sarg/keyboard/photos/IMG_20200824_121157.jpg

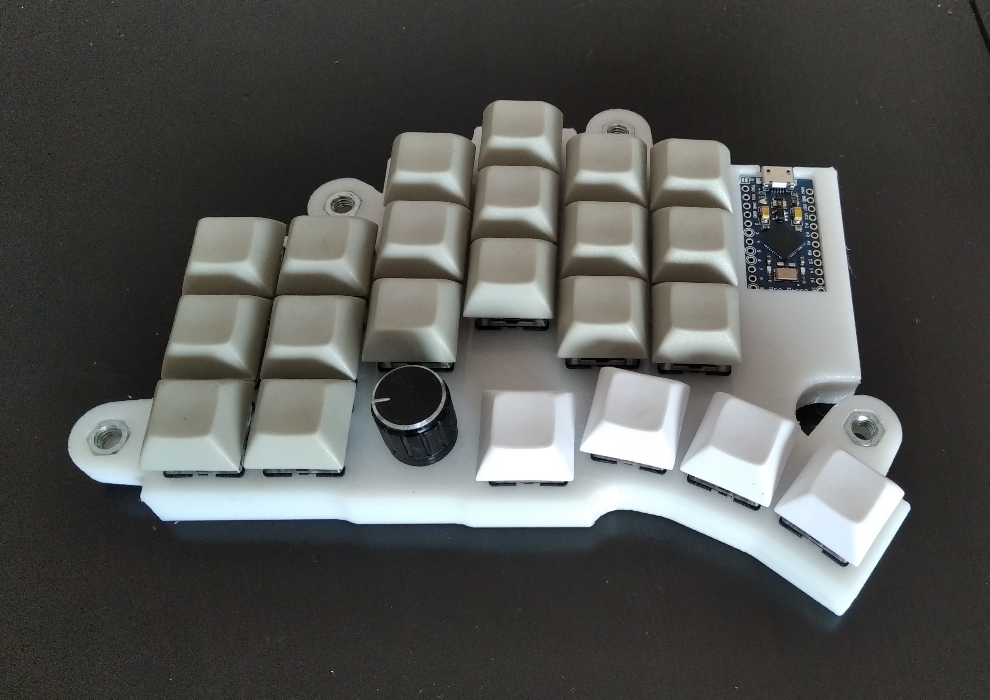
photos/IMG_20200824_121157.jpg
