sarg/keyboard/photos/IMG_20200903_161421.jpg

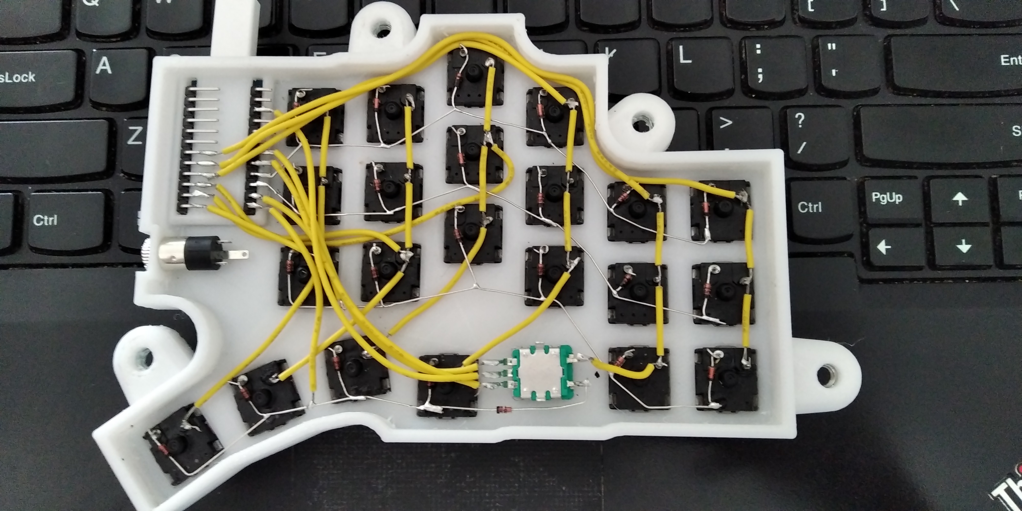
photos/IMG_20200903_161421.jpg
