sarg/keyboard/photos/IMG_20200907_170027.jpg

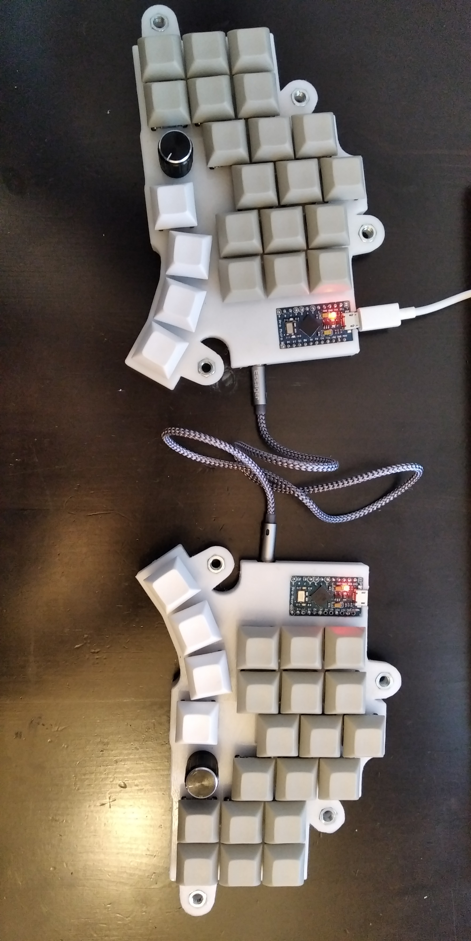
photos/IMG_20200907_170027.jpg
