sarg/keyboard/write_eeprom/keymap.h

const KEY keys[] = {
  { 0, 0, 0, KC_ESC, NO },
  { 0, 0, 1, KC_Q, NO },
  { 0, 0, 2, KC_W, NO },
  { 0, 0, 3, KC_E, NO },
  { 0, 0, 4, KC_R, NO },
  { 0, 0, 5, KC_T, NO },
  { 0, 1, 0, KC_TAB, NO },
  { 0, 1, 1, KC_A, NO },
  { 0, 1, 2, LALT_T(KC_S), NO },
  { 0, 1, 3, LCTL_T(KC_D), NO },
  { 0, 1, 4, LSFT_T(KC_F), NO },
  { 0, 1, 5, KC_G, NO },
  { 0, 2, 0, KC_MINS, NO },
  { 0, 2, 1, KC_Z, NO },
  { 0, 2, 2, KC_X, NO },
  { 0, 2, 3, KC_C, NO },
  { 0, 2, 4, KC_V, NO },
  { 0, 2, 5, KC_B, NO },
  { 0, 3, 1, KC_ENT, NO },
  { 0, 3, 2, KC_MYCM, NO },
  { 0, 3, 3, KC_LALT, NO },
  { 0, 3, 4, MO(1), NO },
  { 0, 3, 5, LGUI_T(KC_ENT), NO },
  { 0, 4, 0, KC_BSPC, NO },
  { 0, 4, 1, KC_P, NO },
  { 0, 4, 2, KC_O, NO },
  { 0, 4, 3, KC_I, NO },
  { 0, 4, 4, KC_U, NO },
  { 0, 4, 5, KC_Y, NO },
  { 0, 5, 0, KC_QUOT, NO },
  { 0, 5, 1, KC_SCLN, NO },
  { 0, 5, 2, RALT_T(KC_L), NO },
  { 0, 5, 3, RCTL_T(KC_K), NO },
  { 0, 5, 4, RSFT_T(KC_J), NO },
  { 0, 5, 5, KC_H, NO },
  { 0, 6, 0, KC_BSLS, NO },
  { 0, 6, 1, KC_SLSH, NO },
  { 0, 6, 2, KC_DOT, NO },
  { 0, 6, 3, KC_COMM, NO },
  { 0, 6, 4, KC_M, NO },
  { 0, 6, 5, KC_N, NO },
  { 0, 7, 1, KC_ENT, NO },
  { 0, 7, 2, KC_RGUI, NO },
  { 0, 7, 3, KC_RALT, NO },
  { 0, 7, 4, MO(2), NO },
  { 0, 7, 5, RALT_T(KC_SPC), NO },
  { 1, 0, 0, KC_GRV, NO },
  { 1, 0, 1, KC_1, NO },
  { 1, 0, 2, KC_2, NO },
  { 1, 0, 3, KC_3, NO },
  { 1, 0, 4, KC_4, NO },
  { 1, 0, 5, KC_5, NO },
  { 1, 1, 0, KC_NO, NO },
  { 1, 1, 1, KC_NO, NO },
  { 1, 1, 2, KC_NO, NO },
  { 1, 1, 3, KC_PGUP, NO },
  { 1, 1, 4, KC_PGDN, NO },
  { 1, 1, 5, KC_NO, NO },
  { 1, 2, 0, KC_F1, NO },
  { 1, 2, 1, KC_F2, NO },
  { 1, 2, 2, KC_F3, NO },
  { 1, 2, 3, KC_F4, NO },
  { 1, 2, 4, KC_F5, NO },
  { 1, 2, 5, KC_F6, NO },
  { 1, 3, 1, QK_BOOT, NO },
  { 1, 3, 2, KC_NO, NO },
  { 1, 3, 3, TO(3), NO },
  { 1, 3, 4, KC_NO, NO },
  { 1, 3, 5, KC_NO, NO },
  { 1, 4, 0, KC_MINS, NO },
  { 1, 4, 1, KC_0, NO },
  { 1, 4, 2, KC_9, NO },
  { 1, 4, 3, KC_8, NO },
  { 1, 4, 4, KC_7, NO },
  { 1, 4, 5, KC_6, NO },
  { 1, 5, 0, KC_NO, NO },
  { 1, 5, 1, KC_NO, NO },
  { 1, 5, 2, KC_RGHT, NO },
  { 1, 5, 3, KC_UP, NO },
  { 1, 5, 4, KC_DOWN, NO },
  { 1, 5, 5, KC_LEFT, NO },
  { 1, 6, 0, KC_F12, NO },
  { 1, 6, 1, KC_F11, NO },
  { 1, 6, 2, KC_F10, NO },
  { 1, 6, 3, KC_F9, NO },
  { 1, 6, 4, KC_F8, NO },
  { 1, 6, 5, KC_F7, NO },
  { 1, 7, 1, KC_MPLY, NO },
  { 1, 7, 2, KC_NO, NO },
  { 1, 7, 3, KC_NO, NO },
  { 1, 7, 4, KC_LGUI, NO },
  { 1, 7, 5, KC_RSFT, NO },
  { 2, 0, 0, KC_TILD, NO },
  { 2, 0, 1, KC_EXLM, NO },
  { 2, 0, 2, KC_AT, NO },
  { 2, 0, 3, KC_HASH, NO },
  { 2, 0, 4, KC_DLR, NO },
  { 2, 0, 5, KC_PERC, NO },
  { 2, 1, 0, KC_NO, NO },
  { 2, 1, 1, KC_NO, NO },
  { 2, 1, 2, KC_NO, NO },
  { 2, 1, 3, KC_NO, NO },
  { 2, 1, 4, KC_NO, NO },
  { 2, 1, 5, KC_NO, NO },
  { 2, 2, 0, KC_NO, NO },
  { 2, 2, 1, KC_NO, NO },
  { 2, 2, 2, KC_NO, NO },
  { 2, 2, 3, KC_NO, NO },
  { 2, 2, 4, KC_NO, NO },
  { 2, 2, 5, KC_NO, NO },
  { 2, 3, 1, KC_NO, NO },
  { 2, 3, 2, KC_NO, NO },
  { 2, 3, 3, KC_NO, NO },
  { 2, 3, 4, KC_NO, NO },
  { 2, 3, 5, KC_LSFT, NO },
  { 2, 4, 0, KC_NO, NO },
  { 2, 4, 1, KC_ASTR, NO },
  { 2, 4, 2, KC_RPRN, NO },
  { 2, 4, 3, KC_LPRN, NO },
  { 2, 4, 4, KC_AMPR, NO },
  { 2, 4, 5, KC_CIRC, NO },
  { 2, 5, 0, KC_NO, NO },
  { 2, 5, 1, KC_NO, NO },
  { 2, 5, 2, KC_RBRC, NO },
  { 2, 5, 3, KC_LBRC, NO },
  { 2, 5, 4, KC_EQL, NO },
  { 2, 5, 5, KC_MINS, NO },
  { 2, 6, 0, KC_NO, NO },
  { 2, 6, 1, KC_NO, NO },
  { 2, 6, 2, KC_RCBR, NO },
  { 2, 6, 3, KC_LCBR, NO },
  { 2, 6, 4, KC_PLUS, NO },
  { 2, 6, 5, KC_UNDS, NO },
  { 2, 7, 1, KC_NO, NO },
  { 2, 7, 2, KC_NO, NO },
  { 2, 7, 3, KC_NO, NO },
  { 2, 7, 4, KC_NO, NO },
  { 2, 7, 5, KC_NO, NO },
  { 3, 0, 0, KC_ESC, NO },
  { 3, 0, 1, KC_7, NO },
  { 3, 0, 2, KC_8, NO },
  { 3, 0, 3, KC_1, NO },
  { 3, 0, 4, KC_2, NO },
  { 3, 0, 5, KC_3, NO },
  { 3, 1, 0, KC_GRV, NO },
  { 3, 1, 1, KC_9, NO },
  { 3, 1, 2, KC_LEFT, NO },
  { 3, 1, 3, KC_UP, NO },
  { 3, 1, 4, KC_RGHT, NO },
  { 3, 1, 5, KC_4, NO },
  { 3, 2, 0, TO(0), NO },
  { 3, 2, 1, KC_0, NO },
  { 3, 2, 2, KC_Q, NO },
  { 3, 2, 3, KC_DOWN, NO },
  { 3, 2, 4, KC_6, NO },
  { 3, 2, 5, KC_5, NO },
  { 3, 3, 1, KC_NO, NO },
  { 3, 3, 2, KC_ENT, NO },
  { 3, 3, 3, KC_TRNS, NO },
  { 3, 3, 4, KC_C, NO },
  { 3, 3, 5, KC_SPC, NO },
  { 3, 4, 0, KC_NO, NO },
  { 3, 4, 1, KC_NO, NO },
  { 3, 4, 2, KC_NO, NO },
  { 3, 4, 3, KC_NO, NO },
  { 3, 4, 4, KC_NO, NO },
  { 3, 4, 5, KC_NO, NO },
  { 3, 5, 0, KC_NO, NO },
  { 3, 5, 1, KC_NO, NO },
  { 3, 5, 2, KC_NO, NO },
  { 3, 5, 3, KC_NO, NO },
  { 3, 5, 4, KC_NO, NO },
  { 3, 5, 5, KC_NO, NO },
  { 3, 6, 0, KC_NO, NO },
  { 3, 6, 1, KC_NO, NO },
  { 3, 6, 2, KC_NO, NO },
  { 3, 6, 3, KC_NO, NO },
  { 3, 6, 4, KC_NO, NO },
  { 3, 6, 5, KC_NO, NO },
  { 3, 7, 1, KC_NO, NO },
  { 3, 7, 2, KC_NO, NO },
  { 3, 7, 3, KC_NO, NO },
  { 3, 7, 4, KC_NO, NO },
  { 3, 7, 5, KC_NO, NO }
};

const ENCODER encoders[] = {
  { 0, 0, false, KC_PGUP, NO },
  { 0, 0, true, KC_PGDN, NO },
  { 0, 1, false, KC_UP, NO },
  { 0, 1, true, KC_DOWN, NO },
  { 1, 0, false, KC_VOLD, NO },
  { 1, 0, true, KC_VOLU, NO },
  { 1, 1, false, KC_VOLD, NO },
  { 1, 1, true, KC_VOLU, NO },
  { 2, 0, false, KC_MEDIA_PREV_TRACK, NO },
  { 2, 0, true, KC_MEDIA_NEXT_TRACK, NO },
  { 2, 1, false, KC_UP, NO },
  { 2, 1, true, KC_DOWN, NO },
  { 3, 0, false, KC_NO, NO },
  { 3, 0, true, KC_NO, NO },
  { 3, 1, false, KC_NO, NO },
  { 3, 1, true, KC_NO, NO }
};
